kostasl/pipettingRobot/ToManufacture/1002_Z_Mount_Plate.stl

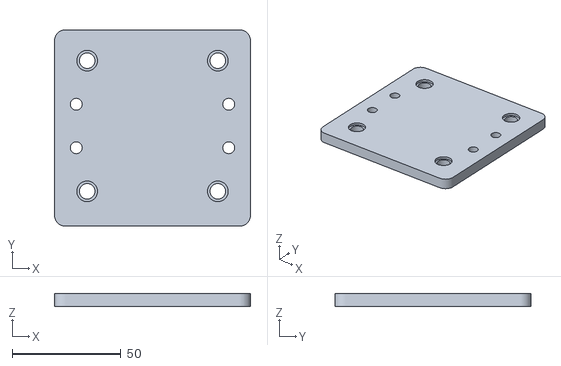
[picture p15: CAD file, 2018-10-01]
ToManufacture/1002_Z_Mount_Plate.stl
90.0 x 90.1 x 6.00
