kostasl/pipettingRobot/ToManufacture/Pipette_Mount2.stl

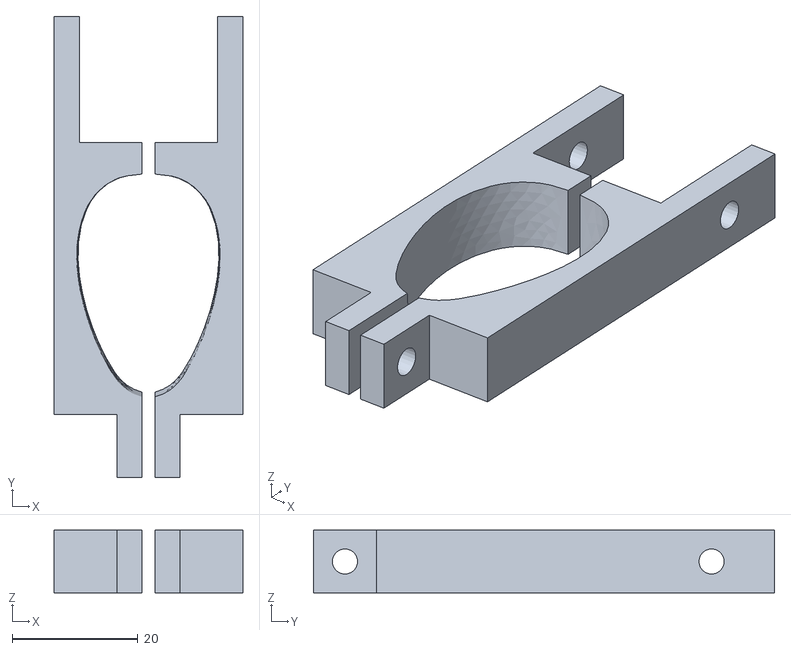
[picture p16: CAD file, 2018-10-01]
ToManufacture/Pipette_Mount2.stl
30.0 x 73.2 x 10.00
