kostasl/pipettingRobot/ToManufacture/PipettePress.stl

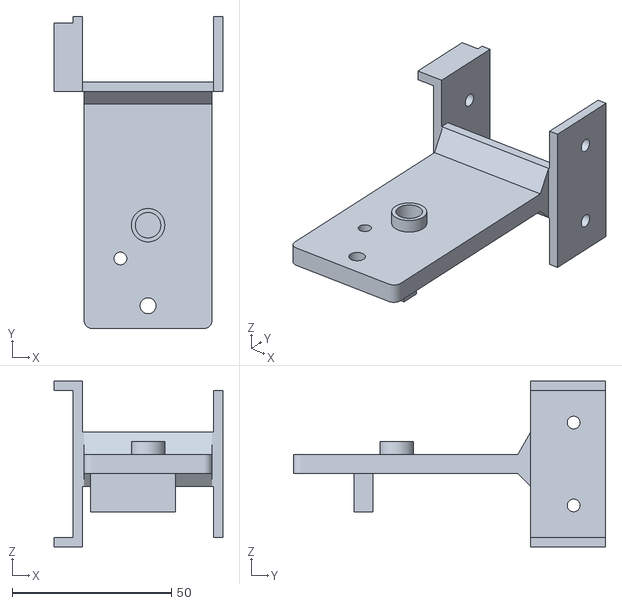
[picture p17: CAD file, 2018-10-01]
ToManufacture/PipettePress.stl
53.0 x 97.9 x 52.0
