kostasl/pipettingRobot/ToManufacture/Powersource_Mount.stl

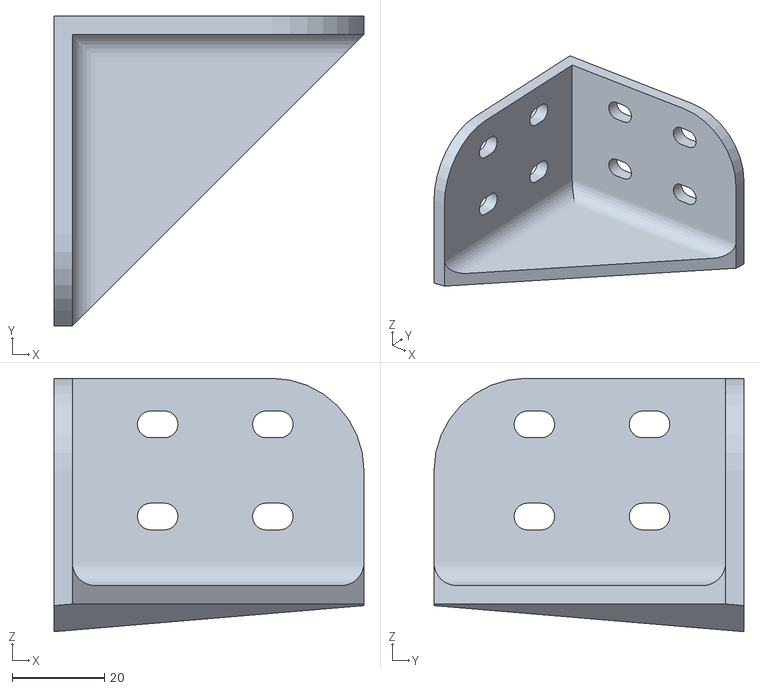
[picture p18: CAD file, 2018-10-01]
ToManufacture/Powersource_Mount.stl
67.3 x 67.3 x 55.0
